Bouhafs-Aek/github.io/kicad/tools/gen_project.py

#!/usr/bin/env python3
"""Generate the KiCad project, schematic and board for the SWRA117D test board.

Everything is derived from two sources of truth that live next to it:

  * ``library/SWRA117D_RF.kicad_sym``   - the antenna symbol
  * ``library/SWRA117D_RF.pretty/*``    - the antenna, SMA and 0402 footprints

The symbol and footprints are parsed and embedded into the schematic and the
board exactly as KiCad would do it, so the three files always agree on pins,
pads and nets.  Run it once; after that KiCad owns the files:

    python3 kicad/tools/gen_project.py
"""

from __future__ import annotations

import copy
import json
import math
import pathlib
import sys
import uuid

sys.path.insert(0, str(pathlib.Path(__file__).resolve().parent))
from line_impedance import synthesise_microstrip  # noqa: E402
from sexpr import Sym, dumps, find, num, parse  # noqa: E402

HERE = pathlib.Path(__file__).resolve().parent
PRJ_DIR = HERE.parent
LIB_DIR = PRJ_DIR / "library"
FP_DIR = LIB_DIR / "SWRA117D_RF.pretty"
PROJECT = "swra117d_2g4_antenna"
LIB_NICK = "SWRA117D_RF"

NAMESPACE = uuid.UUID("6d0c4a55-3a1e-5f2b-8c77-2b9d6e0a4413")


def U(*parts: str) -> str:
    return str(uuid.uuid5(NAMESPACE, "/".join(parts)))


ROOT_UUID = U("sheet", "root")

# ---------------------------------------------------------------- board data
BOARD_X0, BOARD_Y0, BOARD_X1 = 100.0, 60.0, 140.0
BOARD_H = 30.0              # board height; the ground plane is the antenna's
BOARD_Y1 = BOARD_Y0 + BOARD_H            # counterpoise, so shrinking this to
ANT_ORIGIN = (124.0, 66.5)  # antenna feed pad on the board
FEED_X = ANT_ORIGIN[0]      # the feed runs straight down from it to the SMA

# Retune, when there is a trustworthy resonance to retune against.
#
# Uniform in-plane scaling is the retune whose physics needs no model of the
# meander: scale every dimension and gap by k and the resonance moves as 1/k.
# The board ran on a x1.155 scaled radiator for one commit, from an RFsim
# result of 2.83 GHz - but that run had the copper zones unfilled (so the
# antenna had no ground plane, and an inverted-F radiates against its plane)
# and used RFsim's 1.6 mm FR-4 preset instead of this board's 0.8 mm stackup.
# Two errors pulling opposite ways, so the number cannot be used.  Back to the
# published geometry until a valid run says otherwise; see the README for the
# four RFsim settings that make a run valid.  To apply a retune: generate the
# scaled footprint with tools/scale_footprint.py, then set both lines below.
ANT_SCALE = 1.0
ANT_FOOTPRINT = "Texas_SWRA117D_2.4GHz_Left"
W_NECK = 0.5                # neck into the 0.5 mm antenna feed pad
SUB_H, SUB_ER, SUB_TAND = 1.6, 4.5, 0.02   # the board is 1.6 mm FR4

# The feed width is not a chosen number: it is whatever gives 50 ohm on the
# stackup above, so changing the stackup changes it.  Rounded to 0.05 mm
# because no fab holds better than that on an outer layer.
W50 = round(synthesise_microstrip(50.0, SUB_H, SUB_ER, 0.035) / 0.05) * 0.05
POUR_GAP = round(1.25 * SUB_H, 2)   # top pour keep-away either side of the line
LAUNCH_GAP = 2.0            # coplanar gap at the connector: 49.8 ohm on this stackup
LAUNCH_OFFSET = W50 / 2 + LAUNCH_GAP + 1.5      # centre of each SMA ground pad
PAD_LEN_IN = 3.5            # how far the SMA pads reach in from the board edge
TAPER_LEN, TAPER_STEPS = 4.5, 6     # 50 ohm line down to the 0.5 mm feed pad

# The pi network, at the antenna end of the 50 ohm line.  AN058 section 3.4:
# "it is recommended to add a pi-matching network so that the antenna can
# always be matched.  If the antenna design is adequately matched then it just
# takes one zero ohm resistor or DC block cap to be inserted".  SWRA117D says
# this antenna is already a 50 ohm design and publishes no matching values, so
# the series position carries a 0 ohm link and the two shunts are laid out
# empty - somewhere to compensate an enclosure, which AN058's own measurements
# say will detune it downwards.
#
# The line is NOT necked down to the pads.  A 0402 land is 0.56 mm wide, which
# is 103 ohm on this stackup, but only 0.5 mm long: 2.6 degrees at 2.45 GHz.
# Narrowing the line to match the pads would trade that for several
# millimetres of genuinely wrong impedance.
Z3_AT = (FEED_X + 3.0, 72.5)        # shunt, antenna side
Z2_AT = (FEED_X, 76.0)              # series, the 0 ohm link
Z1_AT = (FEED_X + 3.0, 79.5)        # shunt, connector side
PAD_DX = 0.48                       # 0402 land, pad centre offset
# How far short of the series pad the wide line stops.  KiCad tracks have
# round caps, so a 2.95 mm track bulges W50/2 past its endpoint: ending it on
# the pad centre would put that bulge across the opposite pad, 0.96 mm away.
# Stopping 2.0 mm short leaves the cap reaching 0.525 mm into its own pad and
# 0.725 mm clear of the other one.
Z2_STANDOFF = 2.0
PI_BOX = (FEED_X - 4.0, 70.5, FEED_X + 5.5, 81.5)
PI_VIA_DX = 4.9                     # shunt ground vias, inside the box

NETS = {"": 0, "GND": 1, "ANT_FEED": 2, "RF_IN": 3}


def plane_edge() -> float:
    """Top edge of the ground plane, taken from the antenna's keep-out box.

    The footprint draws its required clear area on Dwgs.User; the bottom of
    that box is where the ground plane may start.  Reading it here means a
    rescaled antenna moves the plane edge with it instead of silently
    overlapping copper the antenna needs kept clear.
    """
    fp = parse((FP_DIR / f"{ANT_FOOTPRINT}.kicad_mod").read_text())
    ys = [float(node[i][2])
          for node in fp if isinstance(node, list) and node[0] == "fp_line"
          and str(find(node, "layer")[1]) == "Dwgs.User"
          for i in (1, 2)]
    return ANT_ORIGIN[1] + max(ys)


GND_EDGE_Y = plane_edge()

TITLE = ("2.45 GHz PCB antenna (TI SWRA117D/AN043) - radiator on a 50 ohm SMA "
         "port, pi network fitted as a 0 ohm link")

# reference, library id, value, footprint, schematic placement, board placement
PARTS = [
    dict(ref="J1", lib=f"{LIB_NICK}:Conn_Coaxial_SMA", value="SMA edge launch",
         fp="SMA_EdgeMount_Generic", sch=(76.2, 88.9, 0),
         pcb=(FEED_X, BOARD_Y1, 90),
         nets={"1": "RF_IN", "2": "GND"},
         ref_at=(76.2, 81.28), val_at=(76.2, 83.82),
         desc="Coaxial connector, 50 ohm test port"),
    dict(ref="Z1", lib=f"{LIB_NICK}:C", value="DNP",
         fp="Chip_0402_1005Metric_RF", sch=(88.9, 92.71, 0),
         pcb=(Z1_AT[0], Z1_AT[1], 0), nets={"1": "RF_IN", "2": "GND"},
         ref_at=(91.44, 91.44), val_at=(91.44, 93.98), dnp=True, in_bom=False,
         desc="Pi network, shunt on the connector side. Not fitted: SWRA117D "
              "publishes no matching values for this antenna. Laid out because "
              "AN058 asks for somewhere to compensate an enclosure"),
    dict(ref="Z2", lib=f"{LIB_NICK}:R", value="0R",
         fp="Chip_0402_RF_WideLand", sch=(101.6, 88.9, 90),
         pcb=(Z2_AT[0], Z2_AT[1], 0), nets={"1": "RF_IN", "2": "ANT_FEED"},
         ref_at=(99.06, 85.09), val_at=(99.06, 82.55),
         desc="Pi network, series. 0 ohm link: AN058 section 3.4 - an already "
              "matched antenna 'just takes one zero ohm resistor or DC block "
              "cap'. A 100 pF is the drop-in alternative where the radio needs "
              "DC isolation, which this antenna's DC short to ground makes "
              "worth checking"),
    dict(ref="Z3", lib=f"{LIB_NICK}:C", value="DNP",
         fp="Chip_0402_1005Metric_RF", sch=(114.3, 92.71, 0),
         pcb=(Z3_AT[0], Z3_AT[1], 0), nets={"1": "ANT_FEED", "2": "GND"},
         ref_at=(116.84, 91.44), val_at=(116.84, 93.98), dnp=True, in_bom=False,
         desc="Pi network, shunt on the antenna side. Not fitted, same reason "
              "as Z1"),
    dict(ref="AE1", lib=f"{LIB_NICK}:ANT_SWRA117D_2G4_Left",
         value="ANT_SWRA117D_2G4_Left", fp=ANT_FOOTPRINT,
         sch=(127.0, 81.28, 0), pcb=ANT_ORIGIN + (0,),
         nets={"1": "ANT_FEED", "2": "GND"},
         ref_at=(132.08, 77.47), val_at=(132.08, 80.01),
         fp_ref_at=(-6.0, 1.6), in_bom=False,
         desc="2.45 GHz printed inverted-F antenna (TI SWRA117D, left layout)"
              + (f", geometry scaled x{ANT_SCALE:g}" if ANT_SCALE != 1.0 else ""),
         extra_props=[
             ("Sim.Device", "SUBCKT"),
             ("Sim.Name", "ANT_SWRA117D_2G4"),
             ("Sim.Library", "${KIPRJMOD}/sim/antenna_swra117d.lib"),
             ("Sim.Pins", "1=1 2=2"),
         ]),
]

WIRES = [
    ((81.28, 88.9), (97.79, 88.9)),      # J1 signal -> Z2 pin 1
    ((105.41, 88.9), (127.0, 88.9)),     # Z2 pin 2 -> antenna feed
    ((127.0, 88.9), (127.0, 86.36)),     # up into AE1 pin 1
    ((76.2, 93.98), (76.2, 96.52)),      # J1 shell -> GND
    ((76.2, 96.52), (71.12, 96.52)),     # GND -> PWR_FLAG
    ((88.9, 96.52), (88.9, 99.06)),      # Z1 -> GND
    ((114.3, 96.52), (114.3, 99.06)),    # Z3 -> GND
    ((129.54, 86.36), (129.54, 96.52)),  # AE1 ground pin -> GND
]
JUNCTIONS = [(76.2, 96.52)]
LABELS = [("RF_IN", (85.09, 88.9)), ("ANT_FEED", (110.49, 88.9))]

SCH_NOTE = (
    "TI SWRA117D (AN043) 2.45 GHz printed inverted-F antenna on a 50 ohm port.\n"
    "\n"
    "J1 -> 2.95 mm wide 50 ohm microstrip on 1.6 mm FR4 (er 4.5, tan d 0.02)\n"
    "-> pi network -> AE1 pin 1.  AE1 pin 2 is the inverted-F ground pin and\n"
    "sits on the edge of the ground plane; see the keep-out on the PCB.\n"
    "\n"
    "The pi network carries NO matching values, and that is deliberate.\n"
    "SWRA117D says this antenna is already a 50 ohm design and publishes no\n"
    "matching BOM, so there is no value to fit and inventing one would be\n"
    "fitting copper to a guess.  AN058 section 3.4 asks for the network to\n"
    "exist anyway: 'If the antenna design is adequately matched then it just\n"
    "takes one zero ohm resistor or DC block cap to be inserted into the\n"
    "pi-matching network.'  So:\n"
    "\n"
    "  Z2  0R     series, the link.  100 pF is the drop-in alternative where\n"
    "             the radio needs DC isolation - worth checking here, because\n"
    "             this antenna is a DC short to ground through its own arm.\n"
    "  Z1  DNP    shunt, connector side\n"
    "  Z3  DNP    shunt, antenna side\n"
    "\n"
    "Z1 and Z3 are there because AN058's measurements show an enclosure only\n"
    "ever pulls resonance downwards, and a board with nowhere to compensate\n"
    "that is a board that has to be respun.\n"
    "\n"
    "Simulation: sim/s11_antenna.cir (ngspice, lumped antenna model) and\n"
    "sim/openems/swra117d_openems.py (full wave S11, impedance, far field)."
)

POWER = [  # ground symbols: reference, sheet position
    ("#PWR01", (76.2, 96.52)),
    ("#PWR02", (129.54, 96.52)),
    ("#PWR03", (88.9, 99.06)),
    ("#PWR04", (114.3, 99.06)),
]
# A passive RF board has no power source of its own, so ERC reports
# "Input Power pin not driven by any Output Power pins" on the ground net.
# One flag with a power-output pin on that net is the standard answer.
PWR_FLAGS = [("#FLG01", (71.12, 96.52))]


def effects(size=1.27, hide=False, justify=None, thickness=None):
    font = [Sym("font"), [Sym("size"), num(size), num(size)]]
    if thickness is not None:
        font.append([Sym("thickness"), num(thickness)])
    out = [Sym("effects"), font]
    if justify:
        out.append([Sym("justify")] + [Sym(j) for j in justify.split()])
    if hide:
        out.append([Sym("hide"), Sym("yes")])
    return out


def qualify(fp: str) -> str:
    """A footprint reference as a full lib_id, defaulting to this project's."""
    return fp if ":" in fp else f"{LIB_NICK}:{fp}"


def prop(name, value, at, hide=False, justify=None):
    x, y, rot = at
    return [Sym("property"), name, value,
            [Sym("at"), num(x), num(y), num(rot)],
            effects(hide=hide, justify=justify)]


# ------------------------------------------------------------------ schematic
def lib_symbols() -> list:
    """Embed the symbols this sheet places, exactly as the library defines them.

    KiCad compares every embedded copy against its library and reports
    lib_symbol_mismatch on any difference, so each copy is taken verbatim and
    only the name gains the library nickname.  Symbols the sheet does not
    place are left out, which is what KiCad itself writes.
    """
    used = {part["lib"] for part in PARTS}
    if POWER:
        used.add(f"{LIB_NICK}:GND")
    if PWR_FLAGS:
        used.add(f"{LIB_NICK}:PWR_FLAG")
    out = [Sym("lib_symbols")]
    # grouped by library nickname, so a sheet can place symbols from more than
    # one in-project library and each copy still comes from the file it names
    for nick in sorted({lib_id.split(":", 1)[0] for lib_id in used}):
        lib = parse((LIB_DIR / f"{nick}.kicad_sym").read_text())
        for child in lib[1:]:
            if isinstance(child, list) and child[0] == "symbol":
                lib_id = f"{nick}:{child[1]}"
                if lib_id in used:
                    sym = copy.deepcopy(child)
                    sym[1] = lib_id
                    out.append(sym)
    return out


def sch_symbol(part) -> list:
    x, y, rot = part["sch"]
    ref, value = part["ref"], part["value"]
    node = [Sym("symbol"),
            [Sym("lib_id"), part["lib"]],
            [Sym("at"), num(x), num(y), num(rot)],
            [Sym("unit"), Sym("1")],
            [Sym("exclude_from_sim"), Sym("no")],
            [Sym("in_bom"), Sym("yes" if part.get("in_bom", True) else "no")],
            [Sym("on_board"), Sym("yes")],
            [Sym("dnp"), Sym("yes" if part.get("dnp") else "no")],
            [Sym("uuid"), U("sym", ref)],
            prop("Reference", ref, (*part["ref_at"], 0), justify="left"),
            prop("Value", value, (*part["val_at"], 0), justify="left"),
            prop("Footprint", qualify(part["fp"]), (x, y, 0), hide=True),
            prop("Datasheet", part.get("datasheet", "~"), (x, y, 0), hide=True),
            prop("Description", part["desc"], (x, y, 0), hide=True)]
    for name, value in part.get("extra_props", []):
        node.append(prop(name, value, (x, y, 0), hide=True))
    for pin in sorted(part["nets"]):
        node.append([Sym("pin"), pin, [Sym("uuid"), U("pin", ref, pin)]])
    node.append([Sym("instances"),
                 [Sym("project"), PROJECT,
                  [Sym("path"), f"/{ROOT_UUID}",
                   [Sym("reference"), ref], [Sym("unit"), Sym("1")]]]])
    return node


def sch_power(ref, pos, name="GND", below=True, in_bom=True) -> list:
    """Ground symbol or ERC power flag - both are 'power' symbols with one pin."""
    x, y = pos
    label_y = y + 3.81 if below else y - 3.81
    return [Sym("symbol"),
            [Sym("lib_id"), f"{LIB_NICK}:{name}"],
            [Sym("at"), num(x), num(y), Sym("0")],
            [Sym("unit"), Sym("1")],
            [Sym("exclude_from_sim"), Sym("no" if in_bom else "yes")],
            [Sym("in_bom"), Sym("yes" if in_bom else "no")],
            [Sym("on_board"), Sym("yes" if in_bom else "no")],
            [Sym("dnp"), Sym("no")],
            [Sym("uuid"), U("sym", ref)],
            prop("Reference", ref, (x, y + 6.35, 0), hide=True),
            prop("Value", name, (x, label_y, 0)),
            prop("Footprint", "", (x, y, 0), hide=True),
            prop("Datasheet", "", (x, y, 0), hide=True),
            prop("Description", "Ground reference" if name == "GND"
                 else "ERC power source flag", (x, y, 0), hide=True),
            [Sym("pin"), "1", [Sym("uuid"), U("pin", ref, "1")]],
            [Sym("instances"),
             [Sym("project"), PROJECT,
              [Sym("path"), f"/{ROOT_UUID}",
               [Sym("reference"), ref], [Sym("unit"), Sym("1")]]]]]


def build_schematic() -> list:
    sch = [Sym("kicad_sch"),
           [Sym("version"), Sym("20250114")],
           [Sym("generator"), "gen_project.py"],
           [Sym("generator_version"), "9.0"],
           [Sym("uuid"), ROOT_UUID],
           [Sym("paper"), "A4"],
           [Sym("title_block"),
            [Sym("title"), TITLE],
            [Sym("date"), "2026-09-12"],
            [Sym("rev"), "A"],
            [Sym("comment"), Sym("1"), "Pi network laid out, fitted as a 0 ohm link: no matching values are published for this antenna"],
            [Sym("comment"), Sym("2"), "Antenna keep-out: no copper on any layer"]],
           lib_symbols()]

    for a, b in WIRES:
        sch.append([Sym("wire"),
                    [Sym("pts"), [Sym("xy"), num(a[0]), num(a[1])],
                     [Sym("xy"), num(b[0]), num(b[1])]],
                    [Sym("stroke"), [Sym("width"), Sym("0")], [Sym("type"), Sym("default")]],
                    [Sym("uuid"), U("wire", str(a), str(b))]])
    for x, y in JUNCTIONS:
        sch.append([Sym("junction"),
                    [Sym("at"), num(x), num(y)],
                    [Sym("diameter"), Sym("0")],
                    [Sym("color"), Sym("0"), Sym("0"), Sym("0"), Sym("0")],
                    [Sym("uuid"), U("junction", str((x, y)))]])
    for name, (x, y) in LABELS:
        sch.append([Sym("label"), name,
                    [Sym("at"), num(x), num(y), Sym("0")],
                    effects(justify="left bottom"),
                    [Sym("uuid"), U("label", name)]])
    sch.append([Sym("text"), SCH_NOTE,
                [Sym("exclude_from_sim"), Sym("no")],
                [Sym("at"), num(76.2), num(112.0), Sym("0")],
                effects(size=1.27, justify="left top"),
                [Sym("uuid"), U("text", "note")]])

    for part in PARTS:
        sch.append(sch_symbol(part))
    for ref, pos in POWER:
        sch.append(sch_power(ref, pos))
    for ref, pos in PWR_FLAGS:
        sch.append(sch_power(ref, pos, name="PWR_FLAG", below=False, in_bom=False))

    sch.append([Sym("sheet_instances"), [Sym("path"), "/", [Sym("page"), "1"]]])
    sch.append([Sym("embedded_fonts"), Sym("no")])
    return sch


# ---------------------------------------------------------------------- board
def rotate_at(node, rot):
    """Give a footprint child its absolute text/pad angle."""
    at = find(node, "at")
    if at is None or not rot:
        return
    angle = float(at[3]) if len(at) > 3 else 0.0
    angle = (angle + rot) % 360
    if len(at) > 3:
        at[3] = num(angle)
    else:
        at.append(num(angle))


def rekey_uuids(node, ref: str) -> None:
    for child in node:
        if isinstance(child, list) and child:
            if child[0] == "uuid":
                child[1] = U("fpobj", f"{ref}:{child[1]}")
            else:
                rekey_uuids(child, ref)


def board_footprint(part) -> list:
    # "Name" resolves in this project's default footprint library; "NICK:Name"
    # names another one, which the second antenna's project needs
    nick, _, name = part["fp"].rpartition(":")
    nick = nick or LIB_NICK
    src = parse((LIB_DIR / f"{nick}.pretty" / f"{name}.kicad_mod").read_text())
    x, y, rot = part["pcb"]
    out = [Sym("footprint"), f"{nick}:{src[1]}",
           [Sym("layer"), "F.Cu"],
           [Sym("uuid"), U("fp", part["ref"])],
           [Sym("at"), num(x), num(y)] + ([num(rot)] if rot else [])]
    for child in src[2:]:
        head = child[0]
        if head in ("version", "generator", "generator_version", "layer", "embedded_fonts"):
            continue
        child = copy.deepcopy(child)
        # A library footprint carries its own uuids, and three 0402s placed
        # from one file would otherwise carry three copies of each.  Re-key
        # them from the reference so every object on the board is distinct.
        rekey_uuids(child, part["ref"])
        if head == "property":
            if child[1] == "Reference":
                child[2] = part["ref"]
                if part.get("fp_ref_at"):
                    at = find(child, "at")
                    at[1], at[2] = num(part["fp_ref_at"][0]), num(part["fp_ref_at"][1])
            elif child[1] == "Value":
                child[2] = part["value"]
            rotate_at(child, rot)
            child.append([Sym("unlocked"), Sym("yes")])
        elif head == "fp_text":
            rotate_at(child, rot)
            child.append([Sym("unlocked"), Sym("yes")])
        elif head == "pad":
            rotate_at(child, rot)
            net = part["nets"].get(str(child[1]))
            if net is None:
                raise SystemExit(f"{part['ref']}: no net for pad {child[1]}")
            child.append([Sym("net"), Sym(str(NETS[net])), net])
            child.append([Sym("pinfunction"), net])
            child.append([Sym("pintype"), "passive"])
        out.append(child)
    out += [[Sym("path"), f"/{U('sym', part['ref'])}"],
            [Sym("sheetname"), "Root"],
            [Sym("sheetfile"), f"{PROJECT}.kicad_sch"],
            [Sym("embedded_fonts"), Sym("no")]]
    return out


def in_pi_box(x, y, margin=0.8) -> bool:
    return (PI_BOX[0] - margin <= x <= PI_BOX[2] + margin
            and PI_BOX[1] - margin <= y <= PI_BOX[3] + margin)


def stitch_grid(existing, launch_y, pitch=5.0, keepaway=2.0):
    """A grid of ground vias over the top pour, avoiding everything that matters.

    Skipped: the feed line's pour keep-away corridor, the connector's own
    courtyard (already stitched), anything within *keepaway* of a via that is
    already placed, and a margin from the board edges.
    """
    half = W50 / 2 + POUR_GAP
    out = []
    y = GND_EDGE_Y + 1.5 + pitch
    while y <= BOARD_Y1 - 1.0:
        x = BOARD_X0 + 1.5
        while x <= BOARD_X1 - 1.5:
            in_corridor = FEED_X - half - 0.5 <= x <= FEED_X + half + 0.5
            at_connector = (abs(x - FEED_X) <= 5.3 and y >= launch_y - 2.8)
            crowded = any(math.dist((x, y), pos) < keepaway
                          for pos in existing + out)
            if not (in_corridor or at_connector or crowded or in_pi_box(x, y)):
                out.append((x, y))
            x += pitch
        y += pitch
    return out


def segment(a, b, width, net, layer="F.Cu"):
    return [Sym("segment"),
            [Sym("start"), num(a[0]), num(a[1])],
            [Sym("end"), num(b[0]), num(b[1])],
            [Sym("width"), num(width)],
            [Sym("layer"), layer],
            [Sym("net"), Sym(str(NETS[net]))],
            [Sym("uuid"), U("seg", str(a), str(b), str(width))]]


def via(pos, net="GND", size=0.6, drill=0.3):
    return [Sym("via"),
            [Sym("at"), num(pos[0]), num(pos[1])],
            [Sym("size"), num(size)],
            [Sym("drill"), num(drill)],
            [Sym("layers"), "F.Cu", "B.Cu"],
            [Sym("net"), Sym(str(NETS[net]))],
            [Sym("uuid"), U("via", str(pos))]]


def gr_line(a, b, layer, width=0.1):
    return [Sym("gr_line"),
            [Sym("start"), num(a[0]), num(a[1])],
            [Sym("end"), num(b[0]), num(b[1])],
            [Sym("stroke"), [Sym("width"), num(width)], [Sym("type"), Sym("solid")]],
            [Sym("layer"), layer],
            [Sym("uuid"), U("grline", str(a), str(b), layer)]]


def gr_text(text, pos, layer, size=1.0, thickness=0.15, justify="left"):
    return [Sym("gr_text"), text,
            [Sym("at"), num(pos[0]), num(pos[1]), Sym("0")],
            [Sym("layer"), layer],
            [Sym("uuid"), U("grtext", text, layer)],
            effects(size=size, justify=justify, thickness=thickness)]


def zone_poly(points):
    return [Sym("polygon"),
            [Sym("pts")] + [[Sym("xy"), num(px), num(py)] for px, py in points]]


def gnd_zone(layer, points):
    return [Sym("zone"),
            [Sym("net"), Sym("1")],
            [Sym("net_name"), "GND"],
            [Sym("layer"), layer],
            [Sym("uuid"), U("zone", layer)],
            [Sym("name"), "GND"],
            [Sym("hatch"), Sym("edge"), num(0.508)],
            [Sym("priority"), Sym("0")],
            [Sym("connect_pads"), [Sym("clearance"), num(0.2)]],
            [Sym("min_thickness"), num(0.25)],
            [Sym("filled_areas_thickness"), Sym("no")],
            [Sym("fill"), Sym("yes"),
             [Sym("thermal_gap"), num(0.4)],
             [Sym("thermal_bridge_width"), num(0.4)]],
            zone_poly(points)]


def keepout_zone(name, points, layers=("F.Cu", "B.Cu"), tracks="not_allowed",
                 vias="not_allowed"):
    return [Sym("zone"),
            [Sym("net"), Sym("0")],
            [Sym("net_name"), ""],
            [Sym("layers")] + [str(l) for l in layers],
            [Sym("uuid"), U("zone", name)],
            [Sym("name"), name],
            [Sym("hatch"), Sym("full"), num(0.508)],
            [Sym("connect_pads"), [Sym("clearance"), num(0)]],
            [Sym("min_thickness"), num(0.25)],
            [Sym("filled_areas_thickness"), Sym("no")],
            [Sym("keepout"),
             [Sym("tracks"), Sym(tracks)],
             [Sym("vias"), Sym(vias)],
             [Sym("pads"), Sym("allowed")],
             [Sym("copperpour"), Sym("not_allowed")],
             [Sym("footprints"), Sym("allowed")]],
            [Sym("fill"), [Sym("thermal_gap"), num(0.4)],
             [Sym("thermal_bridge_width"), num(0.4)]],
            zone_poly(points)]


def stackup():
    def layer(name, ltype, thickness=None, material=None, er=None, tand=None):
        node = [Sym("layer"), name, [Sym("type"), ltype]]
        if material:
            node.append([Sym("material"), material])
        if thickness is not None:
            node.append([Sym("thickness"), num(thickness)])
        if er is not None:
            node.append([Sym("epsilon_r"), num(er)])
        if tand is not None:
            node.append([Sym("loss_tangent"), num(tand)])
        return node

    return [Sym("stackup"),
            layer("F.SilkS", "Top Silk Screen"),
            layer("F.Paste", "Top Solder Paste"),
            layer("F.Mask", "Top Solder Mask", thickness=0.01),
            layer("F.Cu", "copper", thickness=0.035),
            layer("dielectric 1", "core", thickness=SUB_H, material="FR4",
                  er=SUB_ER, tand=SUB_TAND),
            layer("B.Cu", "copper", thickness=0.035),
            layer("B.Mask", "Bottom Solder Mask", thickness=0.01),
            layer("B.Paste", "Bottom Solder Paste"),
            layer("B.SilkS", "Bottom Silk Screen"),
            [Sym("copper_finish"), "None"],
            [Sym("dielectric_constraints"), Sym("no")]]


def build_board() -> list:
    layers = [(0, "F.Cu", "signal", None), (31, "B.Cu", "signal", None),
              (32, "B.Adhes", "user", "B.Adhesive"), (33, "F.Adhes", "user", "F.Adhesive"),
              (34, "B.Paste", "user", None), (35, "F.Paste", "user", None),
              (36, "B.SilkS", "user", "B.Silkscreen"), (37, "F.SilkS", "user", "F.Silkscreen"),
              (38, "B.Mask", "user", None), (39, "F.Mask", "user", None),
              (40, "Dwgs.User", "user", "User.Drawings"), (41, "Cmts.User", "user", "User.Comments"),
              (42, "Eco1.User", "user", "User.Eco1"), (43, "Eco2.User", "user", "User.Eco2"),
              (44, "Edge.Cuts", "user", None), (45, "Margin", "user", None),
              (46, "B.CrtYd", "user", "B.Courtyard"), (47, "F.CrtYd", "user", "F.Courtyard"),
              (48, "B.Fab", "user", None), (49, "F.Fab", "user", None)]
    layer_nodes = [Sym("layers")]
    for number, name, ltype, alias in layers:
        node = [Sym(str(number)), name, Sym(ltype)]
        if alias:
            node.append(alias)
        layer_nodes.append(node)

    pcb = [Sym("kicad_pcb"),
           [Sym("version"), Sym("20241229")],
           [Sym("generator"), "gen_project.py"],
           [Sym("generator_version"), "9.0"],
           [Sym("general"), [Sym("thickness"), num(SUB_H + 0.09)],
            [Sym("legacy_teardrops"), Sym("no")]],
           [Sym("paper"), "A4"],
           [Sym("title_block"),
            [Sym("title"), TITLE],
            [Sym("date"), "2026-09-12"],
            [Sym("rev"), "A"],
            [Sym("comment"), Sym("1"), f"2 layer, {SUB_H} mm FR4, 35 um Cu"],
            [Sym("comment"), Sym("2"), f"50 ohm microstrip w = {W50} mm; Z2 = 0R link, Z1 and Z3 not fitted"]],
           layer_nodes,
           [Sym("setup"), stackup(),
            [Sym("pad_to_mask_clearance"), Sym("0")],
            [Sym("allow_soldermask_bridges_in_footprints"), Sym("no")]]]

    for name, number in NETS.items():
        pcb.append([Sym("net"), Sym(str(number)), name])

    for part in PARTS:
        pcb.append(board_footprint(part))

    # board outline
    corners = [(BOARD_X0, BOARD_Y0), (BOARD_X1, BOARD_Y0),
               (BOARD_X1, BOARD_Y1), (BOARD_X0, BOARD_Y1)]
    for i in range(4):
        pcb.append(gr_line(corners[i], corners[(i + 1) % 4], "Edge.Cuts"))

    # ground plane edge marker + notes
    pcb.append(gr_line((BOARD_X0, GND_EDGE_Y), (BOARD_X1, GND_EDGE_Y), "Cmts.User", 0.12))
    pcb.append(gr_text("GND plane edge - no copper above this line on any layer",
                       (BOARD_X0 + 0.8, GND_EDGE_Y - 0.8), "Cmts.User", size=0.9))
    pcb.append(gr_text("ANTENNA KEEP-OUT", (BOARD_X0 + 0.8, 63.2), "F.SilkS", size=1.0))
    pcb.append(gr_text("SWRA117D 2.45 GHz IFA - RF test board",
                       (BOARD_X0 + 1.0, BOARD_Y1 - 7.0), "F.SilkS", size=1.2))
    pcb.append(gr_text(f"50R microstrip w={W50}mm / {SUB_H}mm FR4 er={SUB_ER}",
                       (BOARD_X0 + 1.0, BOARD_Y1 - 5.6), "F.SilkS", size=0.9))

    # 50 ohm feed: the SMA sits on the bottom edge directly below the antenna
    # feed pad and faces it, so the line is one straight run with no corner.
    #
    # On this stackup the 50 ohm line is W50 wide while the antenna's feed pad
    # is 0.5 mm, so the two cannot butt together: the step would be a real
    # discontinuity, and a line that wide would crowd the antenna's ground pin.
    # The last TAPER_LEN mm steps down in TAPER_STEPS stages instead.
    launch_y = BOARD_Y1 - PAD_LEN_IN / 2          # SMA signal pad centre
    taper_top = ANT_ORIGIN[1] + 0.5               # where the 0.5 mm neck starts
    taper_bot = taper_top + TAPER_LEN
    # the 50 ohm run, interrupted by the series pad of the pi network
    tracks = [((FEED_X, launch_y), (FEED_X, Z2_AT[1] + Z2_STANDOFF), W50, "RF_IN"),
              ((FEED_X, Z2_AT[1] - Z2_STANDOFF), (FEED_X, taper_bot), W50, "ANT_FEED")]
    # the two shunt positions: a stub from the line out to the signal pad, and
    # the ground pad on to a via.  The pour is cut away here, so that via is
    # the only route to the plane - which is what makes it the short one.
    for at, net in ((Z1_AT, "RF_IN"), (Z3_AT, "ANT_FEED")):
        # the stub starts on the line's centre line, not on its edge, so it
        # lands on the track rather than merely inside its copper
        tracks.append(((FEED_X, at[1]), (at[0] - PAD_DX, at[1]), 0.6, net))
        tracks.append(((at[0] + PAD_DX, at[1]),
                       (FEED_X + PI_VIA_DX, at[1]), 0.6, "GND"))
    for i in range(TAPER_STEPS):
        y0 = taper_bot - i * TAPER_LEN / TAPER_STEPS
        y1 = taper_bot - (i + 1) * TAPER_LEN / TAPER_STEPS
        width = W50 + (W_NECK - W50) * (i + 0.5) / TAPER_STEPS
        tracks.append(((FEED_X, y0), (FEED_X, y1), round(width, 3), "ANT_FEED"))
    tracks.append(((FEED_X, taper_top), (FEED_X, ANT_ORIGIN[1]), W_NECK, "ANT_FEED"))
    for a, b, width, net in tracks:
        pcb.append(segment(a, b, width, net))

    # Ground stitching, in three jobs.
    #
    # 1. The launch: 8 vias inside the connector's own pads, so the coplanar
    #    ground at the port is tied to the bottom plane right where the
    #    return current has to cross.
    # 2. The plane edge: a fence at 3.0 mm = lambda/19 at 2.45 GHz in FR4,
    #    which stops the plane pair radiating from its open edge.
    # 3. The pour area: a 5.0 mm grid, so no patch of top pour is left big
    #    enough to resonate.  A 22 mm island - which is what each side of
    #    the feed corridor would otherwise be - is half-wave resonant at
    #    3.25 GHz, inside the range this board gets simulated over.  At
    #    5.0 mm the patches resonate above 14 GHz.
    stitch = [(FEED_X + sign * (LAUNCH_OFFSET + dx), launch_y + dy)
              for sign in (-1, 1) for dx in (-1.0, 1.0) for dy in (-0.8, 0.8)]
    stitch += [(FEED_X + PI_VIA_DX, at[1]) for at in (Z1_AT, Z3_AT)]
    stitch += [(x, GND_EDGE_Y + 1.0) for x in
               (103, 106, 109, 112, 115, 118, 121, 127.5, 130.5, 133.5, 136.5)]
    stitch += stitch_grid(stitch, launch_y)
    for pos in stitch:
        pcb.append(via(pos))

    plane = [(BOARD_X0 + 0.2, GND_EDGE_Y), (BOARD_X1 - 0.2, GND_EDGE_Y),
             (BOARD_X1 - 0.2, BOARD_Y1 - 0.2), (BOARD_X0 + 0.2, BOARD_Y1 - 0.2)]
    pcb.append(gnd_zone("F.Cu", plane))
    pcb.append(gnd_zone("B.Cu", plane))
    pcb.append(keepout_zone("ANTENNA_KEEPOUT",
                            [(BOARD_X0 - 0.5, BOARD_Y0 - 0.5), (BOARD_X1 + 0.5, BOARD_Y0 - 0.5),
                             (BOARD_X1 + 0.5, GND_EDGE_Y), (BOARD_X0 - 0.5, GND_EDGE_Y)]))
    # Keep the top pour POUR_GAP away from the 50 ohm line so it stays a
    # microstrip referenced to the bottom plane instead of turning into a
    # narrow-gap coplanar waveguide.  Tracks, vias and pads stay legal.
    # The corridor starts below the plane edge, not at it: the antenna needs a
    # straight ground plane edge, and a notch cut into it right under the feed
    # would become part of the antenna. The line is already necked down there.
    half = W50 / 2 + POUR_GAP
    corridor_top = GND_EDGE_Y + 3.0
    pcb.append(keepout_zone("RF_POUR_KEEPAWAY",
                            [(FEED_X - half, corridor_top), (FEED_X + half, corridor_top),
                             (FEED_X + half, BOARD_Y1 + 0.5), (FEED_X - half, BOARD_Y1 + 0.5)],
                            layers=("F.Cu",), tracks="allowed", vias="allowed"))
    # The pi network needs more room than the line does: the shunt parts reach
    # sideways past the corridor, and their ground pads must not land on the
    # top pour, or they would be grounded before the via rather than through it.
    pcb.append(keepout_zone("PI_NETWORK_CLEARANCE",
                            [(PI_BOX[0], PI_BOX[1]), (PI_BOX[2], PI_BOX[1]),
                             (PI_BOX[2], PI_BOX[3]), (PI_BOX[0], PI_BOX[3])],
                            layers=("F.Cu",), tracks="allowed", vias="allowed"))
    pcb.append([Sym("embedded_fonts"), Sym("no")])
    return pcb


# -------------------------------------------------------------------- project
def build_project() -> dict:
    def netclass(name, clearance, width, priority):
        return {
            "bus_width": 12, "clearance": clearance, "diff_pair_gap": 0.25,
            "diff_pair_via_gap": 0.25, "diff_pair_width": 0.2, "line_style": 0,
            "microvia_diameter": 0.3, "microvia_drill": 0.1, "name": name,
            "pcb_color": "rgba(0, 0, 0, 0.000)", "priority": priority,
            "schematic_color": "rgba(0, 0, 0, 0.000)", "track_width": width,
            "via_diameter": 0.6, "via_drill": 0.3, "wire_width": 6,
        }

    return {
        "board": {
            "3dviewports": [],
            "design_settings": {
                "defaults": {
                    "board_outline_line_width": 0.1,
                    "copper_line_width": 0.2,
                    "copper_text_size_h": 1.0,
                    "copper_text_size_v": 1.0,
                    "copper_text_thickness": 0.15,
                    "other_line_width": 0.15,
                    "silk_line_width": 0.15,
                    "silk_text_size_h": 1.0,
                    "silk_text_size_v": 1.0,
                    "silk_text_thickness": 0.15,
                },
                "diff_pair_dimensions": [],
                "drc_exclusions": [],
                "rules": {
                    "min_clearance": 0.15,
                    "min_copper_edge_clearance": 0.2,
                    "min_hole_clearance": 0.2,
                    "min_microvia_diameter": 0.2,
                    "min_microvia_drill": 0.1,
                    "min_through_hole_diameter": 0.2,
                    "min_track_width": 0.15,
                    "min_via_annular_width": 0.1,
                    "min_via_diameter": 0.5,
                },
                "track_widths": [0.0, 0.25, 0.5, 1.5],
                "via_dimensions": [{"diameter": 0.0, "drill": 0.0},
                                   {"diameter": 0.6, "drill": 0.3}],
            },
            "layer_presets": [],
            "viewports": [],
        },
        "boards": [],
        "cvpcb": {"equivalence_files": []},
        "libraries": {"pinned_footprint_libs": [], "pinned_symbol_libs": []},
        "meta": {"filename": f"{PROJECT}.kicad_pro", "version": 3},
        "net_settings": {
            "classes": [netclass("Default", 0.2, 0.25, 2147483647),
                        netclass("RF_50R", 0.3, W50, 0)],
            "meta": {"version": 4},
            "net_colors": None,
            "netclass_assignments": None,
            "netclass_patterns": [{"netclass": "RF_50R", "pattern": "ANT_FEED"},
                                  {"netclass": "RF_50R", "pattern": "RF_IN"}],
        },
        "pcbnew": {"last_paths": {"gencad": "", "idf": "", "netlist": "",
                                  "plot": "", "pos_files": "", "specctra_dsn": "",
                                  "step": "", "svg": "", "vrml": ""},
                   "page_layout_descr_file": ""},
        "schematic": {"legacy_lib_dir": "", "legacy_lib_list": []},
        "sheets": [[ROOT_UUID, "Root"]],
        "text_variables": {},
    }


def main() -> None:
    sch_path = PRJ_DIR / f"{PROJECT}.kicad_sch"
    pcb_path = PRJ_DIR / f"{PROJECT}.kicad_pcb"
    pro_path = PRJ_DIR / f"{PROJECT}.kicad_pro"
    sch_path.write_text(dumps(build_schematic()) + "\n")
    pcb_path.write_text(dumps(build_board()) + "\n")
    pro_path.write_text(json.dumps(build_project(), indent=2) + "\n")
    for path in (sch_path, pcb_path, pro_path):
        print(f"wrote {path.relative_to(PRJ_DIR.parent)}")


if __name__ == "__main__":
    main()
